kndndrj/renew3d/images/photo_1.jpg

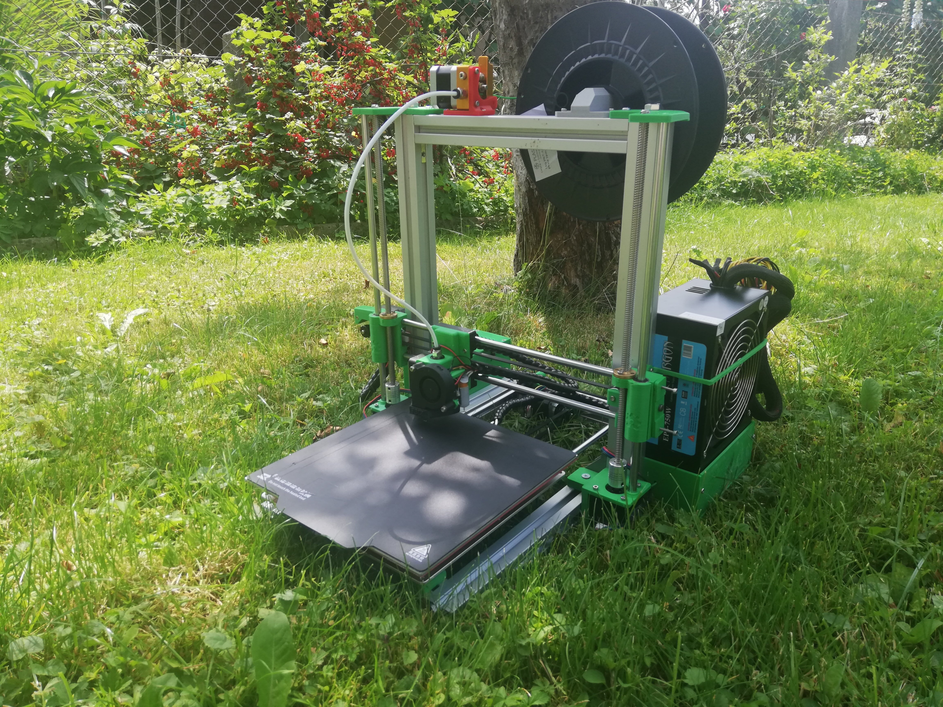
images/photo_1.jpg
