kndndrj/renew3d/images/photo_2.jpg

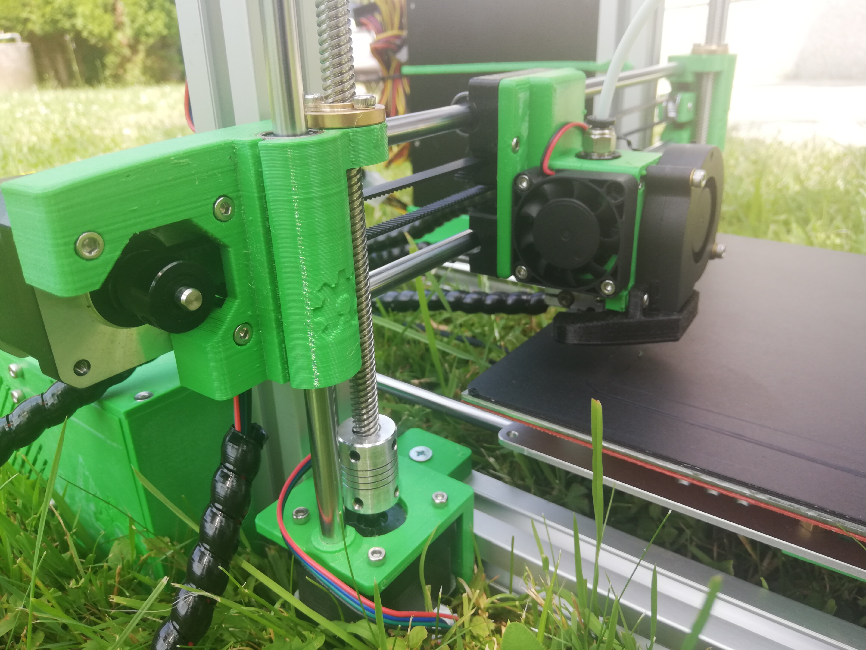
images/photo_2.jpg
