kndndrj/renew3d/images/photo_3.jpg

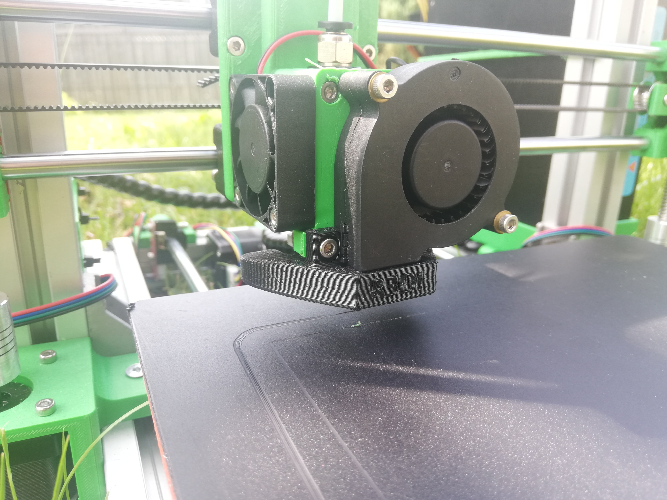
images/photo_3.jpg
