kndndrj/renew3d/cad/printed_parts/main_assembly/stl/ssr_enclosure_left.stl

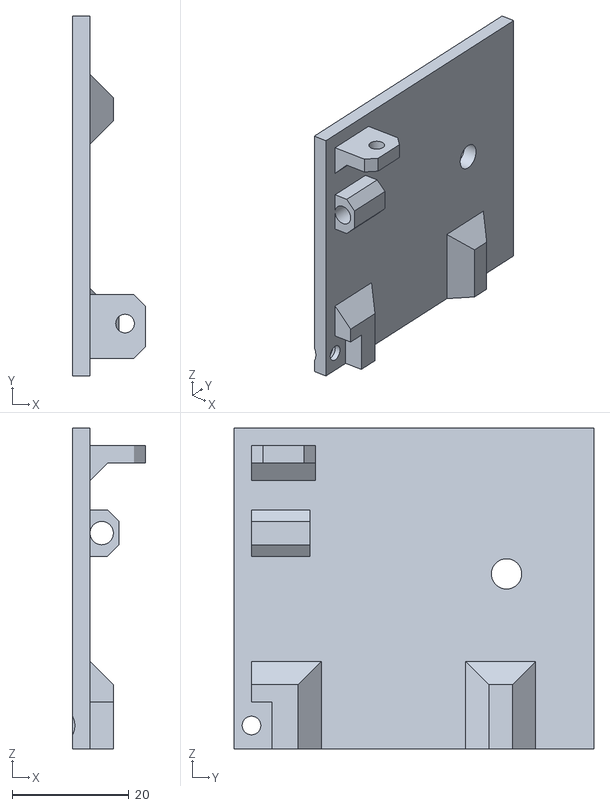
[picture p20: CAD file, 2022-06-08]
cad/printed_parts/main_assembly/stl/ssr_enclosure_left.stl
12.5 x 61.8 x 55.0
