kndndrj/renew3d/cad/printed_parts/main_assembly/step/x_tensioner.step

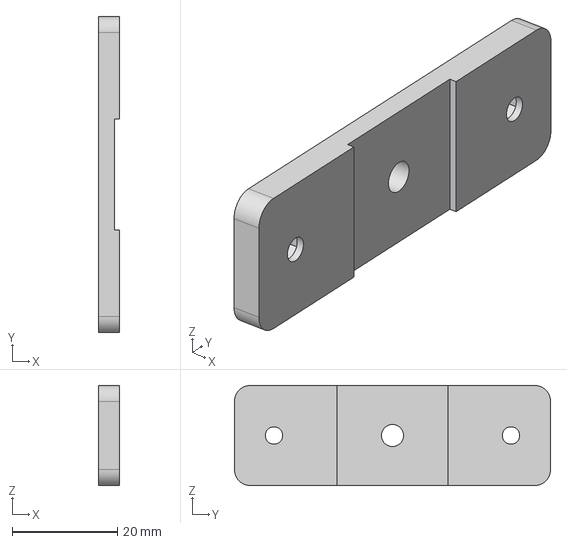
[picture p21: CAD file, 2022-06-08]
cad/printed_parts/main_assembly/step/x_tensioner.step
4.00 x 60.0 x 19.0 mm
