kndndrj/renew3d/cad/printed_parts/main_assembly/stl/ssr_enclosure_bottom.stl

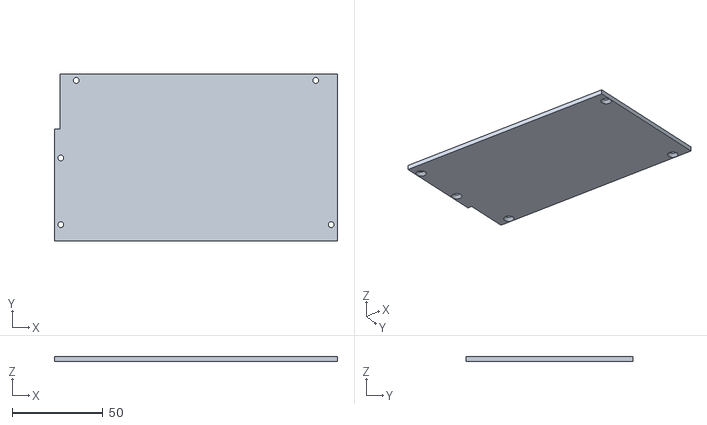
[picture p22: CAD file, 2022-06-08]
cad/printed_parts/main_assembly/stl/ssr_enclosure_bottom.stl
156.0 x 92.0 x 3.00
