kndndrj/renew3d/cad/printed_parts/main_assembly/step/x_idler.step

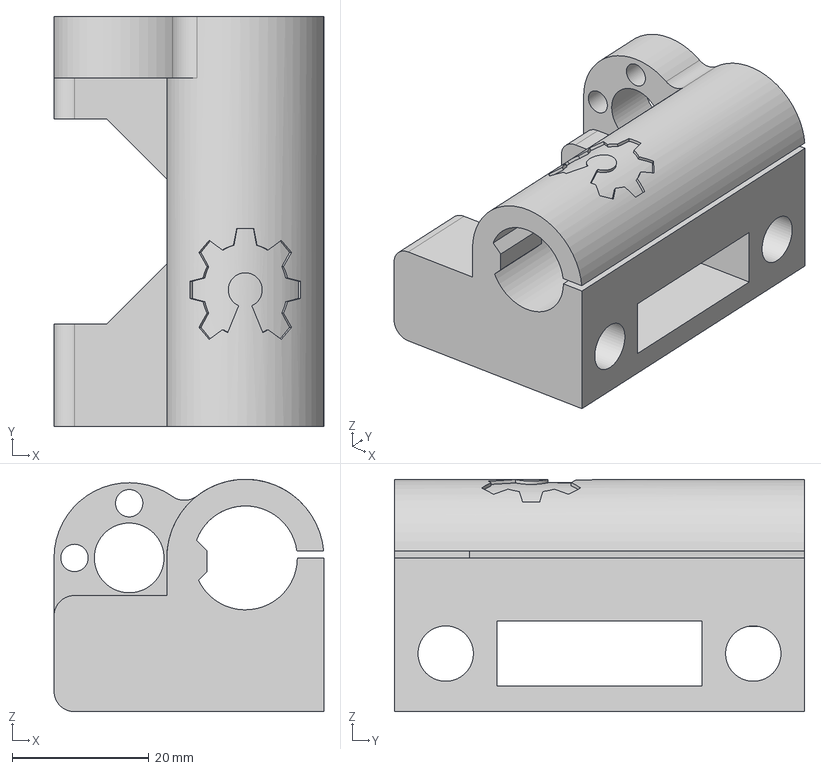
[picture p23: CAD file, 2022-06-08]
cad/printed_parts/main_assembly/step/x_idler.step
39.5 x 60.0 x 34.0 mm
