kndndrj/renew3d/cad/printed_parts/main_assembly/stl/ssr_enclosure_right.stl

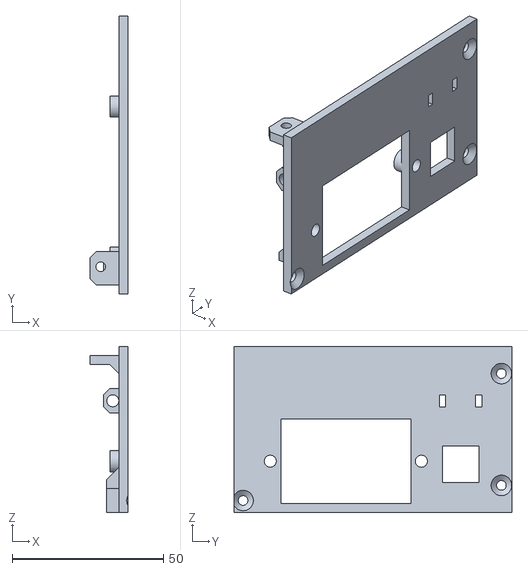
[picture p24: CAD file, 2022-06-08]
cad/printed_parts/main_assembly/stl/ssr_enclosure_right.stl
12.5 x 92.0 x 55.0
