kndndrj/renew3d/cad/printed_parts/main_assembly/step/y_pulley_holder_front.step

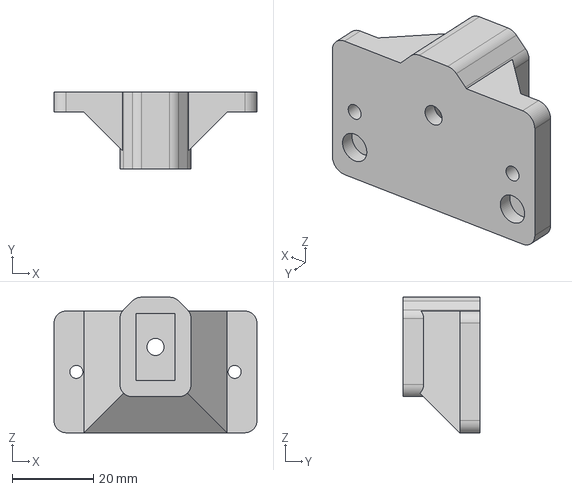
[picture p25: CAD file, 2022-06-08]
cad/printed_parts/main_assembly/step/y_pulley_holder_front.step
50.0 x 19.0 x 33.4 mm
