kndndrj/renew3d/cad/printed_parts/main_assembly/stl/ramps_enclosure_front.stl

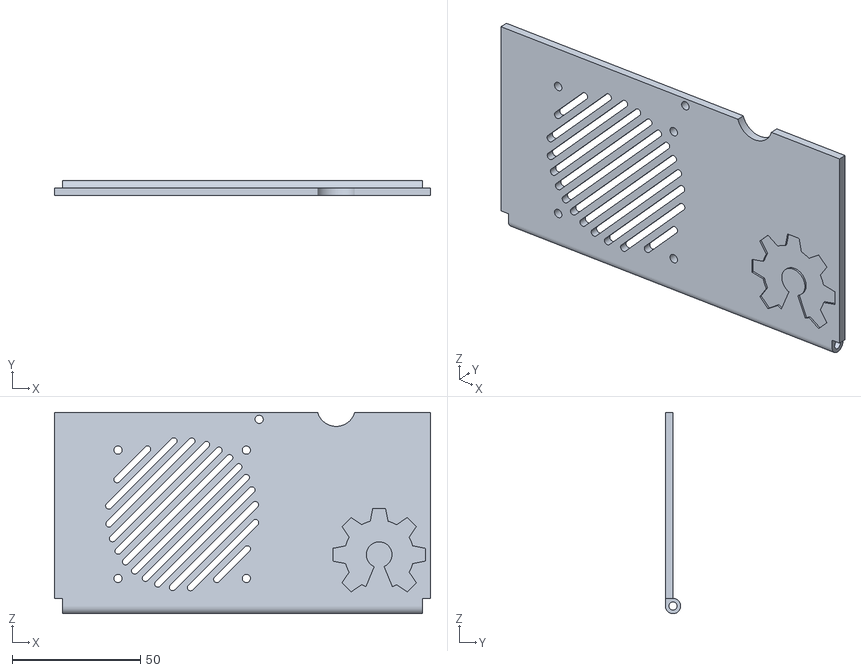
[picture p26: CAD file, 2022-06-08]
cad/printed_parts/main_assembly/stl/ramps_enclosure_front.stl
146.5 x 6.00 x 78.5
