kndndrj/renew3d/cad/printed_parts/main_assembly/step/y_bearing_holder.step

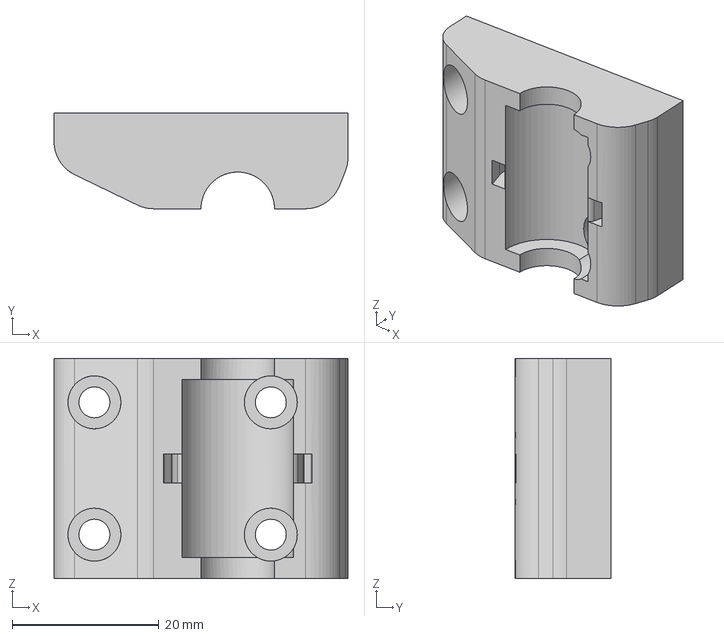
[picture p27: CAD file, 2022-06-08]
cad/printed_parts/main_assembly/step/y_bearing_holder.step
40.0 x 13.0 x 30.0 mm
