kndndrj/renew3d/cad/printed_parts/main_assembly/stl/ramps_enclosure_back.stl

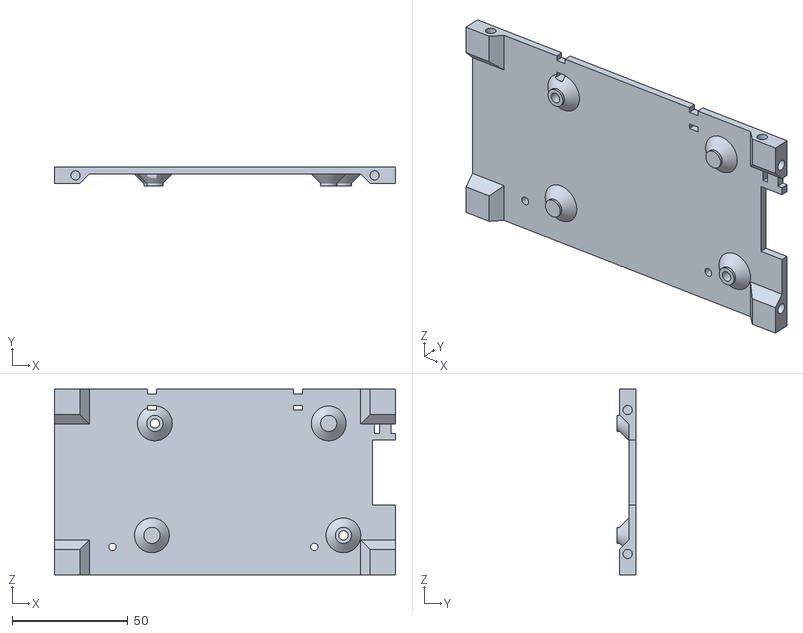
[picture p28: CAD file, 2022-06-08]
cad/printed_parts/main_assembly/stl/ramps_enclosure_back.stl
147.0 x 8.00 x 80.0
