kndndrj/renew3d/cad/printed_parts/main_assembly/step/ssr_enclosure.step

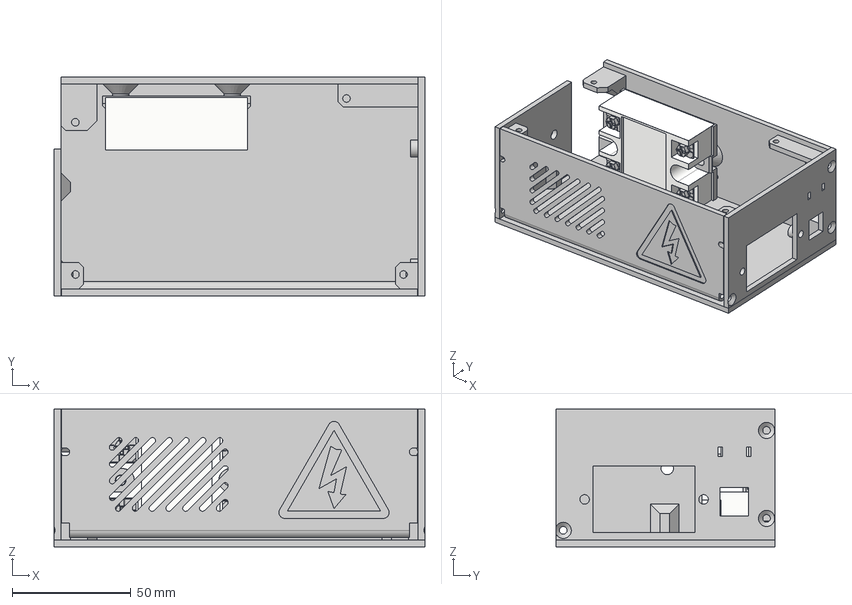
[picture p29: CAD file, 2022-06-08]
cad/printed_parts/main_assembly/step/ssr_enclosure.step
156.0 x 92.0 x 58.0 mm
SSR-40 DA BOTTOM
SSR-40 DA TOP
SSR-40 DA Screw x 4
SSR-40 DA Big Plate x 2
SSR-40 DA Lock Washer x 4
SSR-40 DA Small Plate x 2
