kndndrj/renew3d/cad/printed_parts/main_assembly/step/z_motor_holder_left.step

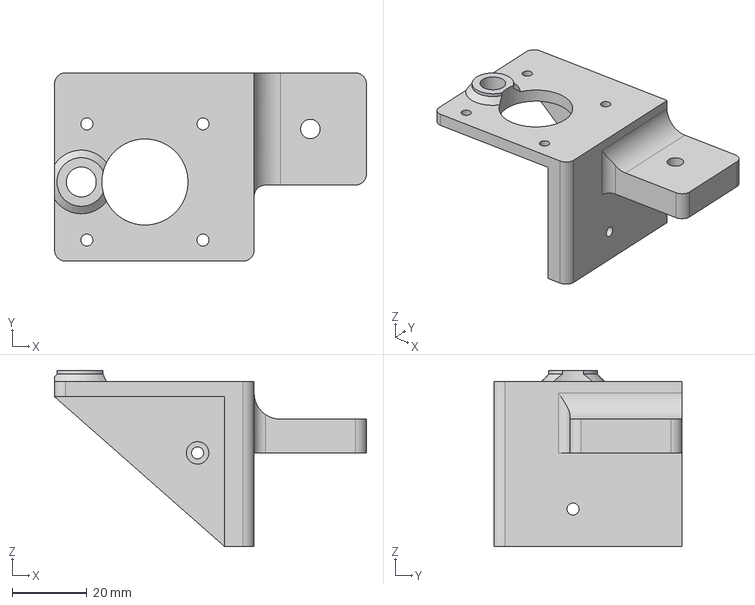
[picture p30: CAD file, 2022-06-08]
cad/printed_parts/main_assembly/step/z_motor_holder_left.step
83.3 x 50.3 x 47.0 mm
