kndndrj/renew3d/cad/printed_parts/main_assembly/step/x_carriage.step

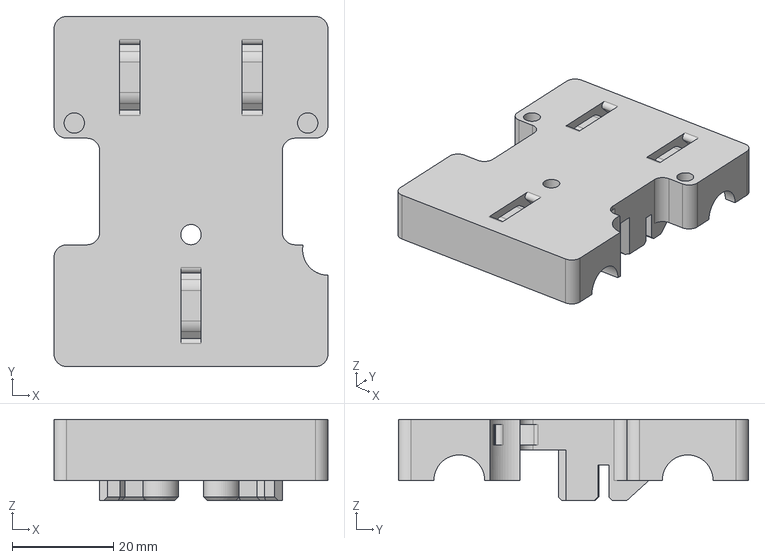
[picture p31: CAD file, 2022-06-08]
cad/printed_parts/main_assembly/step/x_carriage.step
54.0 x 69.0 x 16.0 mm
