kndndrj/renew3d/cad/printed_parts/main_assembly/step/y_belt_holder.step

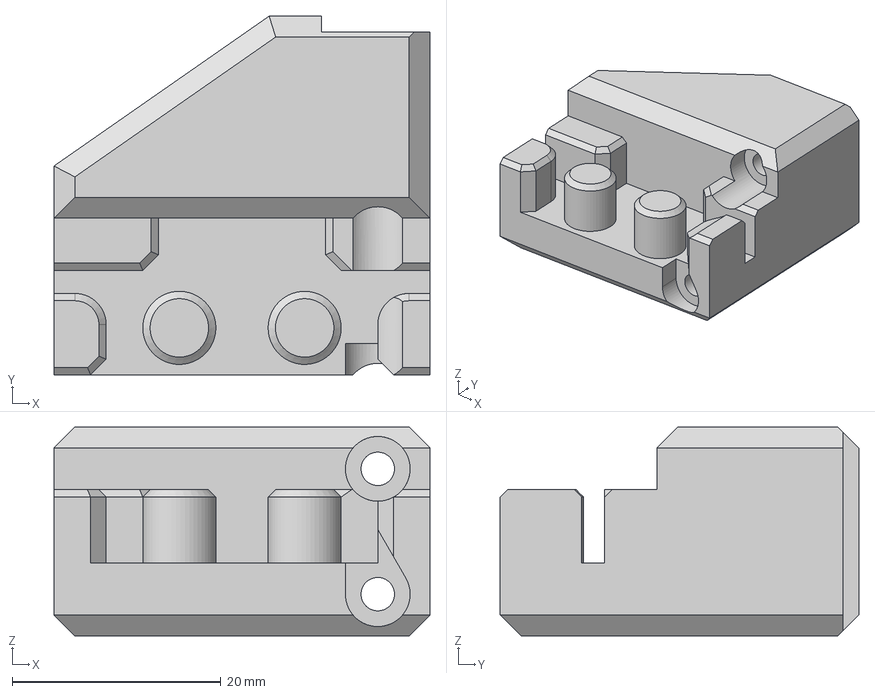
[picture p32: CAD file, 2022-06-08]
cad/printed_parts/main_assembly/step/y_belt_holder.step
36.0 x 34.4 x 20.0 mm
