kndndrj/renew3d/cad/printed_parts/main_assembly/step/y_guide_holder.step

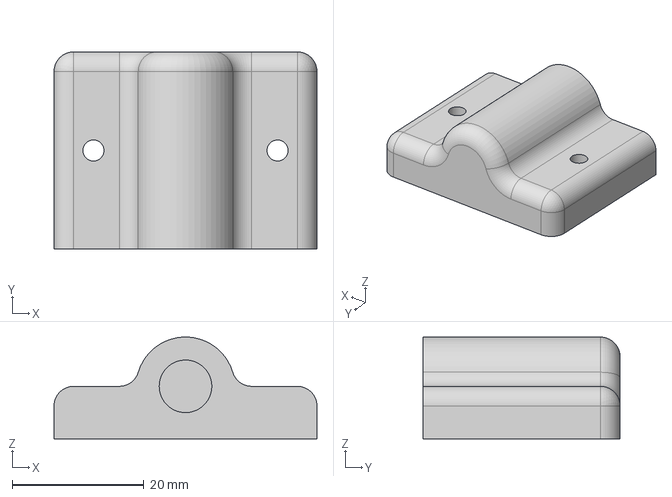
[picture p33: CAD file, 2022-06-08]
cad/printed_parts/main_assembly/step/y_guide_holder.step
40.0 x 30.0 x 15.5 mm
