kndndrj/renew3d/cad/printed_parts/main_assembly/step/part_cooling_fan_duct.step

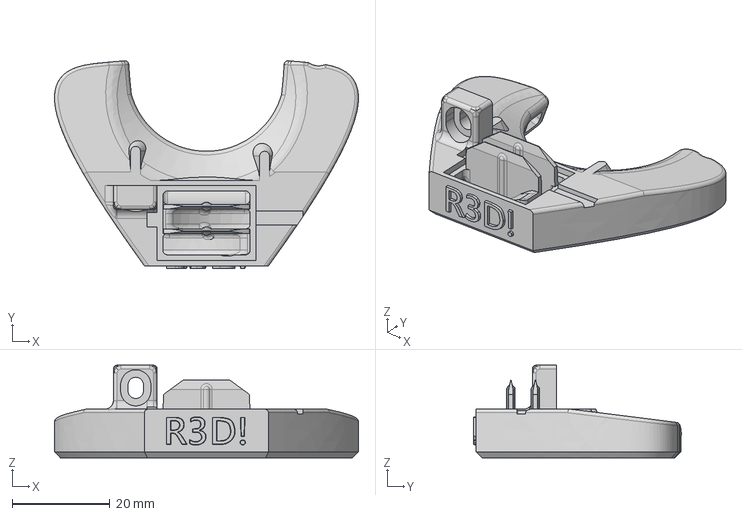
[picture p34: CAD file, 2022-06-08]
cad/printed_parts/main_assembly/step/part_cooling_fan_duct.step
62.3 x 42.6 x 19.0 mm
