kndndrj/renew3d/cad/printed_parts/main_assembly/step/x_motor_holder.step

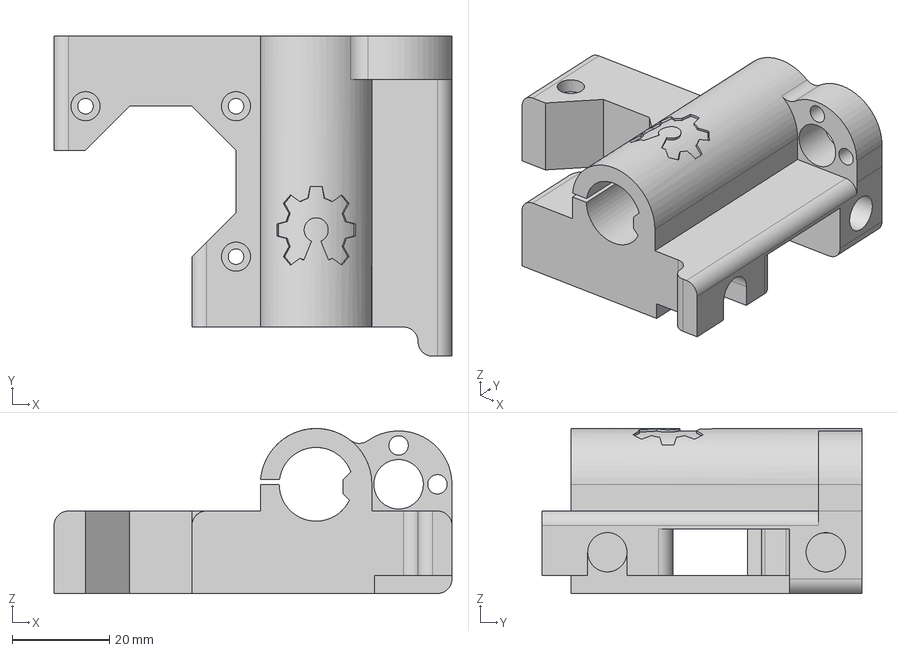
[picture p35: CAD file, 2022-06-08]
cad/printed_parts/main_assembly/step/x_motor_holder.step
82.0 x 66.0 x 34.0 mm
