kndndrj/renew3d/cad/printed_parts/main_assembly/step/hotend_holder_back_induction_probe_12.step

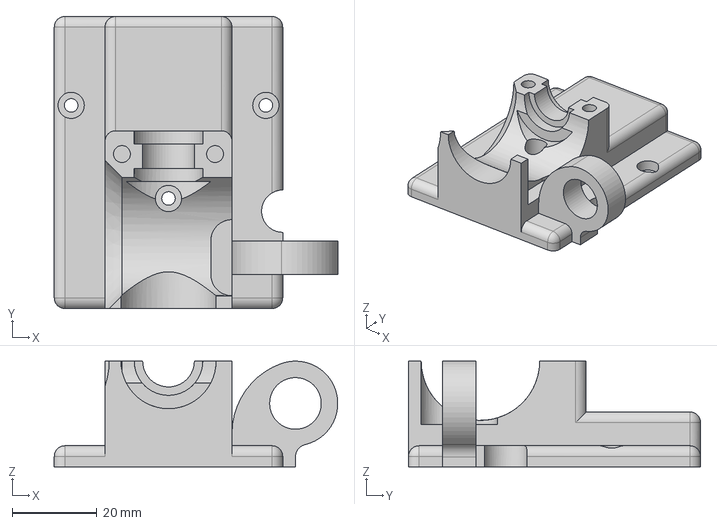
[picture p36: CAD file, 2022-06-08]
cad/printed_parts/main_assembly/step/hotend_holder_back_induction_probe_12.step
67.0 x 69.0 x 25.0 mm
