kndndrj/renew3d/cad/printed_parts/main_assembly/step/y_pulley_holder_back.step

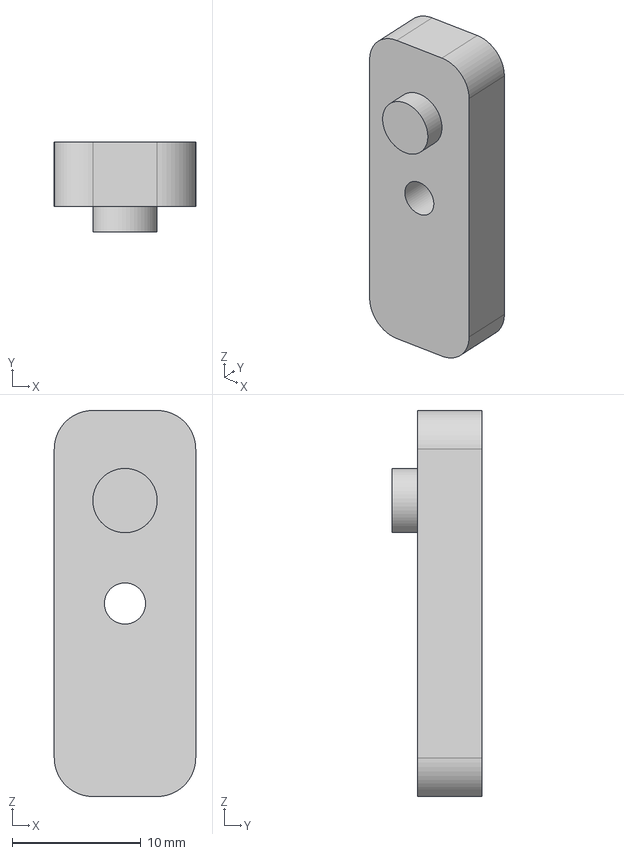
[picture p37: CAD file, 2022-06-08]
cad/printed_parts/main_assembly/step/y_pulley_holder_back.step
11.0 x 7.00 x 30.0 mm
